Legin0007/True-Sight-Glasses/Firmware/Source Code/esp-who/docs/_static/get-started/work_flow_en.png

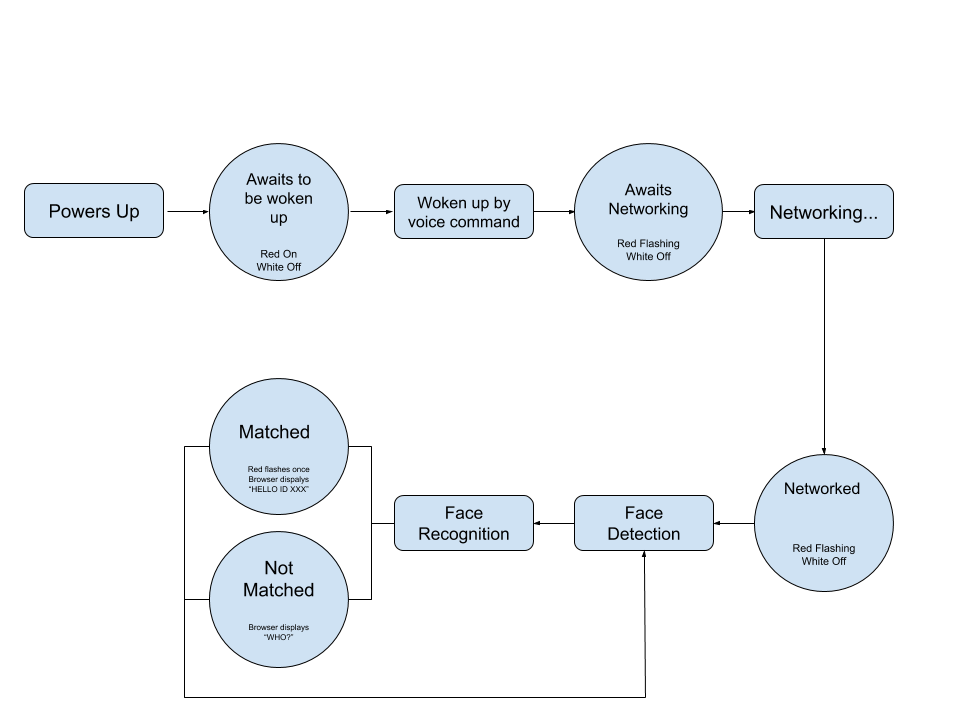
Firmware/Source Code/esp-who/docs/_static/get-started/work_flow_en.png
