Legin0007/True-Sight-Glasses/Firmware/Source Code/esp-who/docs/docs.png

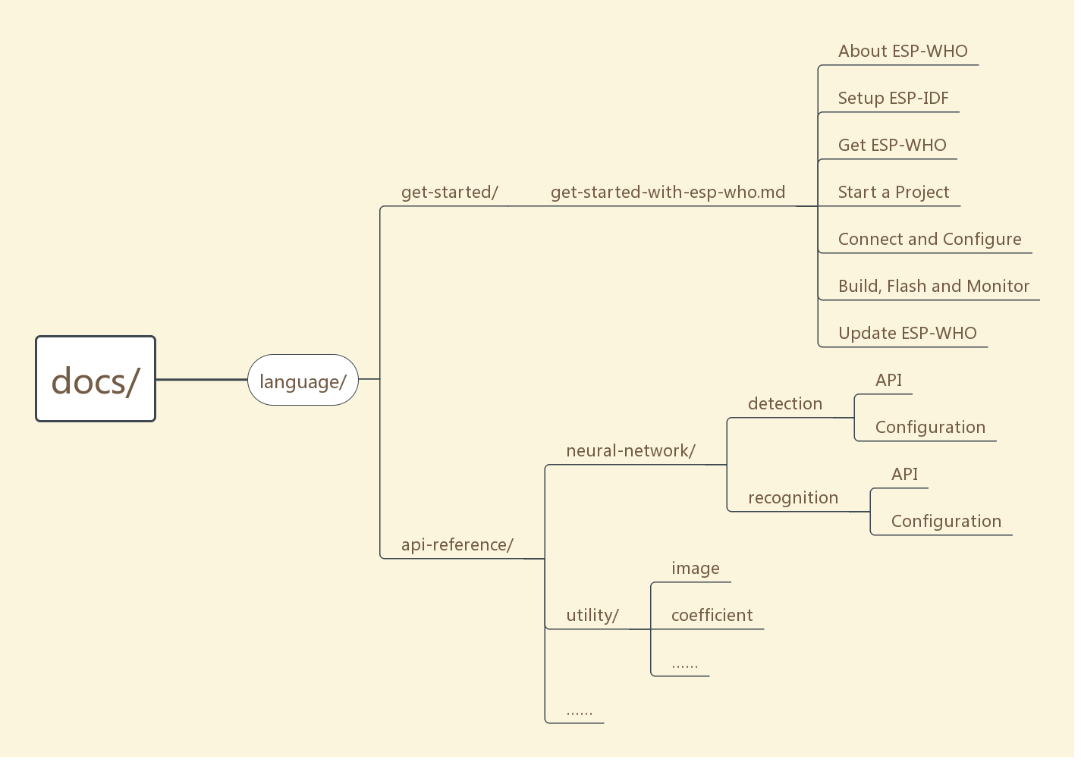
Firmware/Source Code/esp-who/docs/docs.png
