Legin0007/True-Sight-Glasses/Firmware/Source Code/esp-who/img/esp-who_config.png

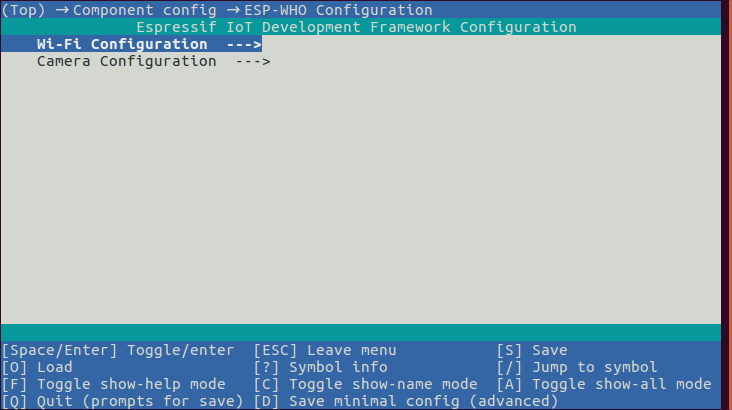
Firmware/Source Code/esp-who/img/esp-who_config.png
