Legin0007/True-Sight-Glasses/Firmware/Source Code/esp-who/img/esp_eye_Wechat_list.jpg

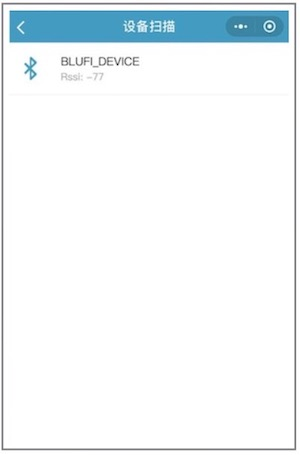
Firmware/Source Code/esp-who/img/esp_eye_Wechat_list.jpg
