Legin0007/True-Sight-Glasses/Firmware/Source Code/esp-who/img/esp_eye_Wechat_network_configuration.jpg

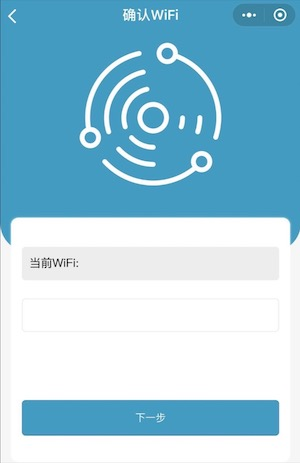
Firmware/Source Code/esp-who/img/esp_eye_Wechat_network_configuration.jpg
