Legin0007/True-Sight-Glasses/Firmware/Source Code/esp-who/img/esp_eye_wechat_qr.jpg

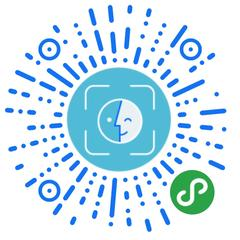
Firmware/Source Code/esp-who/img/esp_eye_wechat_qr.jpg
