Legin0007/True-Sight-Glasses/Firmware/Source Code/esp-who/img/face_recognition_model_config.png

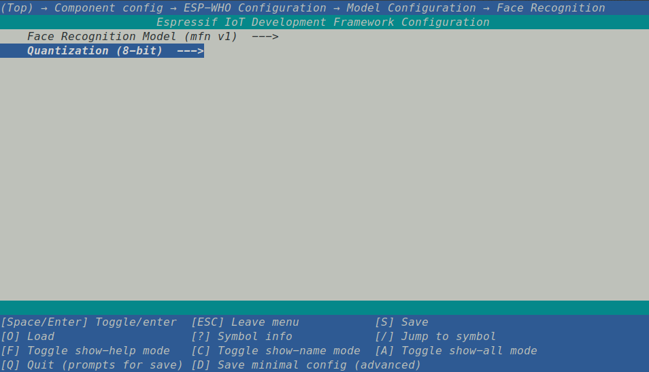
Firmware/Source Code/esp-who/img/face_recognition_model_config.png
